aetel/MiDispositivoMIDI_v2/Pictures/00_green.jpg

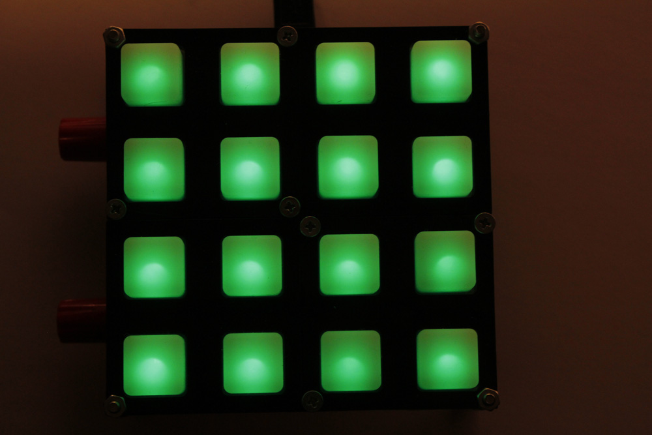
Pictures/00_green.jpg
