aetel/MiDispositivoMIDI_v2/Pictures/00_live_near.jpg

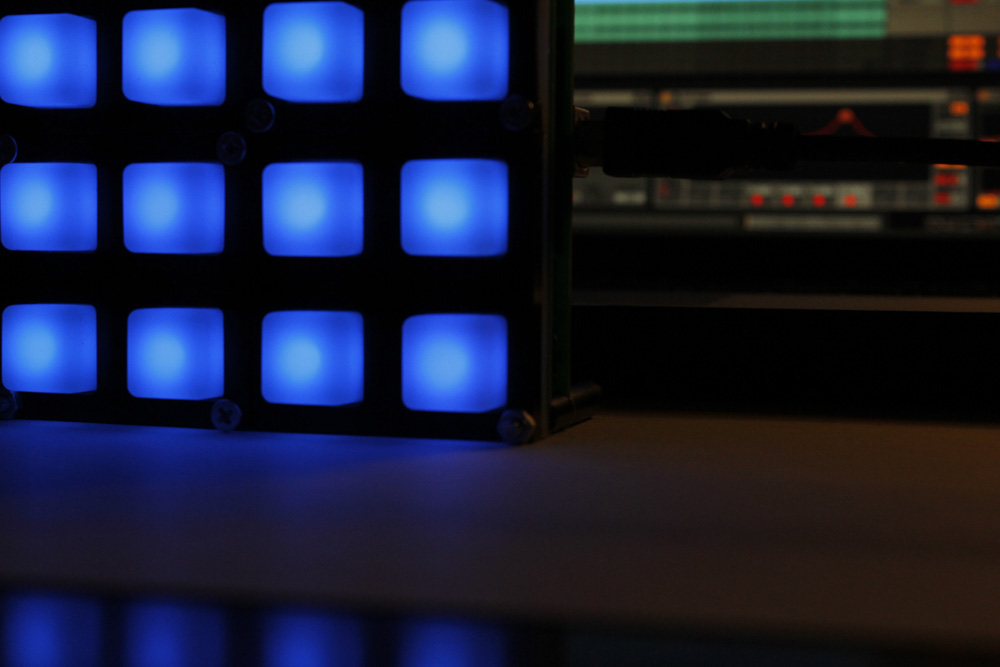
Pictures/00_live_near.jpg
